SteveRMann/CurrentSensor/src/currentSensor/wifi.ino

// setup_wifi
// ============================= Connect the ESP to the router =============================
// Connect to WiFi network so we can reach the MQTT broker and publish messages to topics.

/*
  Make sure you include at the start of the sketch:
  #define hostPrefix "CGM-"       // 6-chars MAX. Used by setup_wifi()
  #include "ESP8266WiFi.h"        // Not needed if also using the Arduino OTA Library...
  #include "D:\River Documents\Arduino\libraries\Kaywinnet.h"  \\ WiFi credentials
  char macBuffer[24];             // Holds the last three digits of the MAC, in hex.
  char hostNamePrefix[] = hostPrefix;
  char hostName[12];              // Holds hostNamePrefix + the last three bytes of the MAC address.
  IPAddress myIP;                 // Holds the IP address
  int rssi;
*/

#ifndef Kaywinnet
#include "D:\River Documents\Arduino\libraries\Kaywinnet.h"  // WiFi credentials
#endif


void setup_wifi() {
  byte mac[6];                     // the MAC address of your Wifi

  Serial.println(F("\n"));
  Serial.print(F("Connecting to "));
  Serial.println(my_ssid);


  WiFi.mode(WIFI_STA);
  WiFi.enableInsecureWEP();
  WiFi.begin(my_ssid, my_password);
  while (WiFi.status() != WL_CONNECTED) {
    delay(500);
    Serial.print(WiFi.status()); Serial.print(F(" "));
  }
  Serial.println(F("\nWiFi connected, "));
  Serial.print(F("MAC Address: "));
  Serial.println(WiFi.macAddress());
  Serial.print(F("IP address: "));
  Serial.println(WiFi.localIP());

  rssi = WiFi.RSSI();
  Serial.print("Signal Strength (RSSI):");
  Serial.println(rssi);
 
  myIP = WiFi.localIP();


  // Get the last three numbers of the mac address.
  // "4C:11:AE:0D:83:86" becomes "0D8386" in macBuffer.
  WiFi.macAddress(mac);
  snprintf(macBuffer, sizeof(macBuffer), "%02X%02X%02X", mac[3], mac[4], mac[5]);

  // Build hostNamePrefix + last three bytes of the MAC address.
  strcpy(hostName, hostNamePrefix);
  strcat(hostName, macBuffer);

  Serial.print(F("hostName = \""));
  Serial.print(hostName);
  Serial.println(F("\""));

  //client.publish(statusTopic, hostName);

}
